ieb/N2KNMEA0183Wifi/pcb/ltspice/Draft1.asc

R1: res; 10K
R3: res; 22K
R4: Res; 4K7
U1: 4N25
U2: PC817A
U3: PC817C
V1: voltage; PULSE(0 5 0.1 0.01 0.01 1 2)
V2: voltage; 10
Named nets: 0
.tran 5s startup
