ieb/N2KNMEA0183Wifi/pcb/ltspice/Isolator.asc

C1: cap; 15p
C2: cap; 0.1µ
R1: res; 3.3K
R6: Res; 10K
U1: 4N25
U2: 4N28
U3: BJT_10mA
U4: 6N137
V1: voltage; 3.3
V2: voltage; PULSE(0 3 0.001 0 0 0.000102 0.000204); Rser=100
V3: voltage; SINE(0 0 200)
V4: voltage; SINE(0 0 147000)
V5: voltage; SINE(3 0 200)
Named nets: 0
.tran 2m startup
